Gonellarro/CO2_Weather_Sensor/imgs/docker-volume-inspect.png

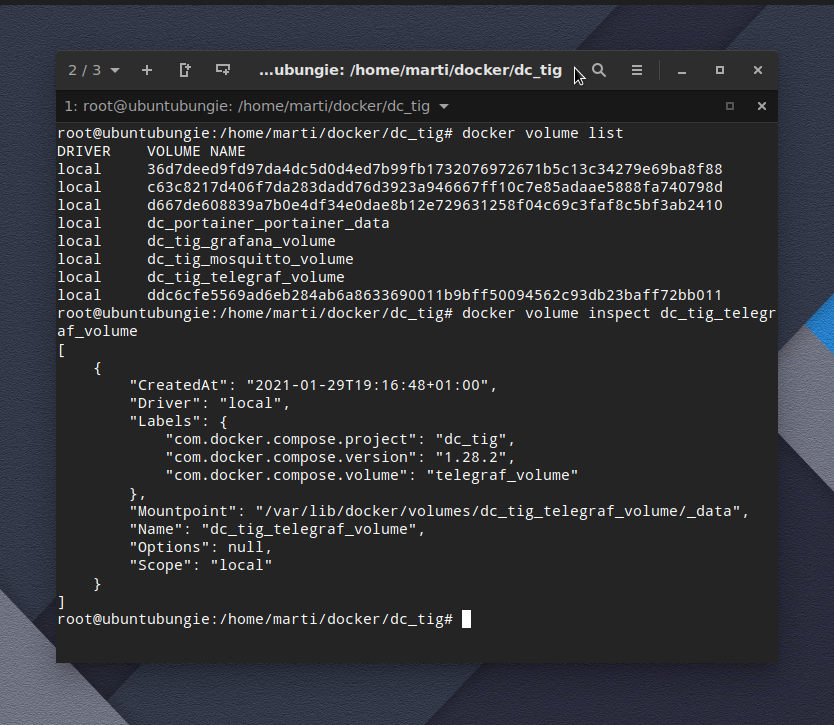
imgs/docker-volume-inspect.png
