Gonellarro/CO2_Weather_Sensor/imgs/docker-volume-list.png

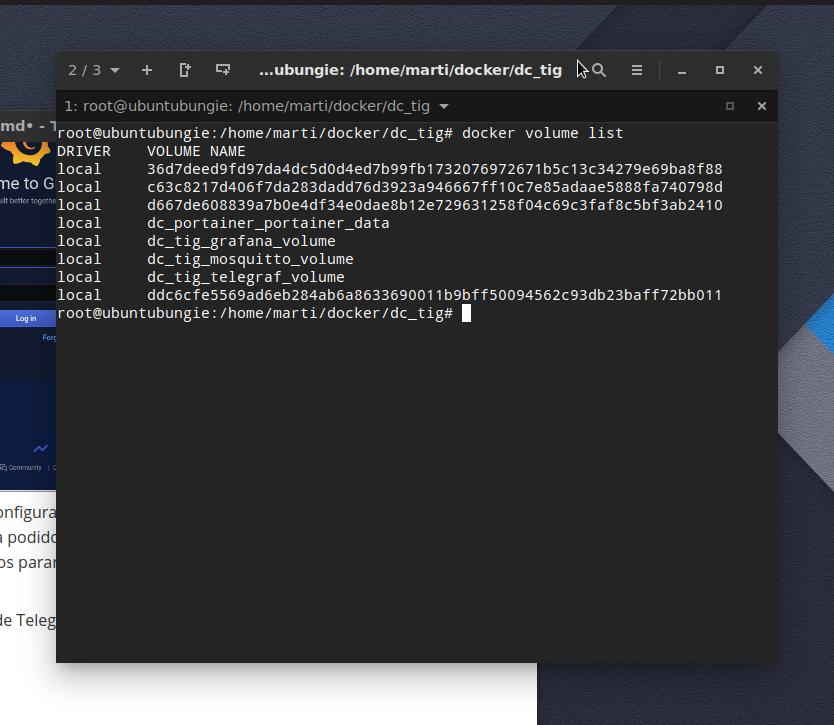
imgs/docker-volume-list.png
